Remiker/lemarConnect/Arduino Devkit/00_Unitary_tests/00_ReadSensors/00_ReadSensors.ino

/*
  MKR ENV Shield - Read Sensors
  This example code is in the public domain.
*/

#include <Arduino_MKRENV.h>

void setup() {
  Serial.begin(9600);
  while (!Serial);

  if (!ENV.begin()) {
    Serial.println("Failed to initialize MKR ENV Shield!");
    while (1);
  }
}

void loop() {
  // read all the sensor values
  float temperature = ENV.readTemperature();
  float humidity    = ENV.readHumidity();
  float pressure    = ENV.readPressure();
  float illuminance = ENV.readIlluminance();
  float uva         = ENV.readUVA();
  float uvb         = ENV.readUVB();
  float uvIndex     = ENV.readUVIndex();

  // print each of the sensor values
  Serial.print("Temperature = ");
  Serial.print(temperature);
  Serial.println(" °C");

  Serial.print("Humidity    = ");
  Serial.print(humidity);
  Serial.println(" %");

  Serial.print("Pressure    = ");
  Serial.print(pressure);
  Serial.println(" kPa");

  Serial.print("Illuminance = ");
  Serial.print(illuminance);
  Serial.println(" lx");

  Serial.print("UVA         = ");
  Serial.println(uva);

  Serial.print("UVB         = ");
  Serial.println(uvb);

  Serial.print("UV Index    = ");
  Serial.println(uvIndex);

  // print an empty line
  Serial.println();

  // wait 1 second to print again
  delay(1000);
}
